LDHydro/meshslide/assets/20260126211406.jpg

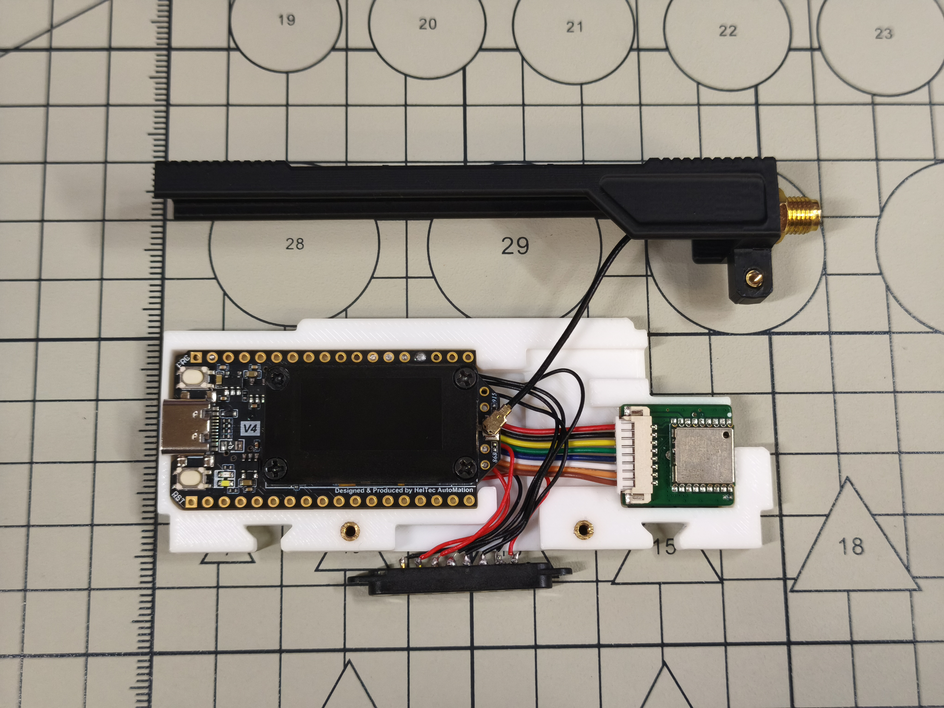
assets/20260126211406.jpg
