LDHydro/meshslide/assets/20260126212053.jpg

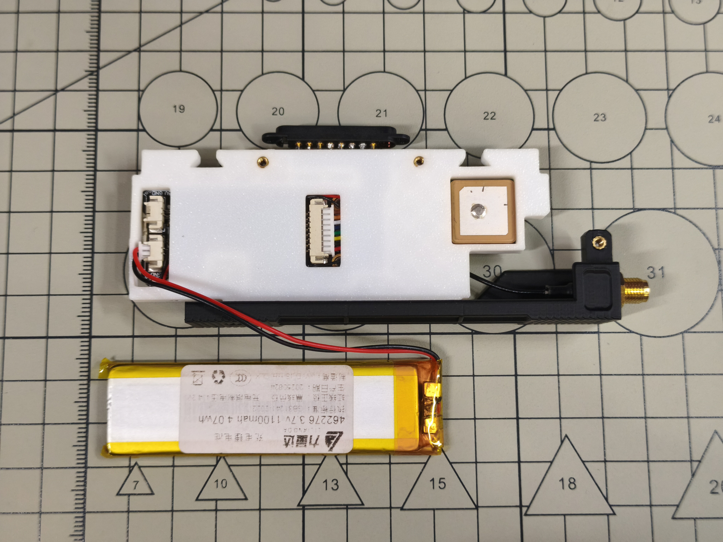
assets/20260126212053.jpg
