LDHydro/meshslide/assets/20260126212810.jpg

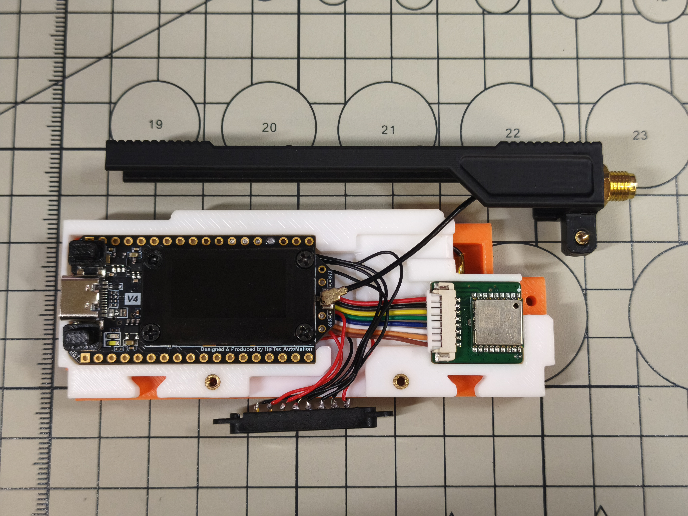
assets/20260126212810.jpg
