LDHydro/meshslide/assets/20260126213025.jpg

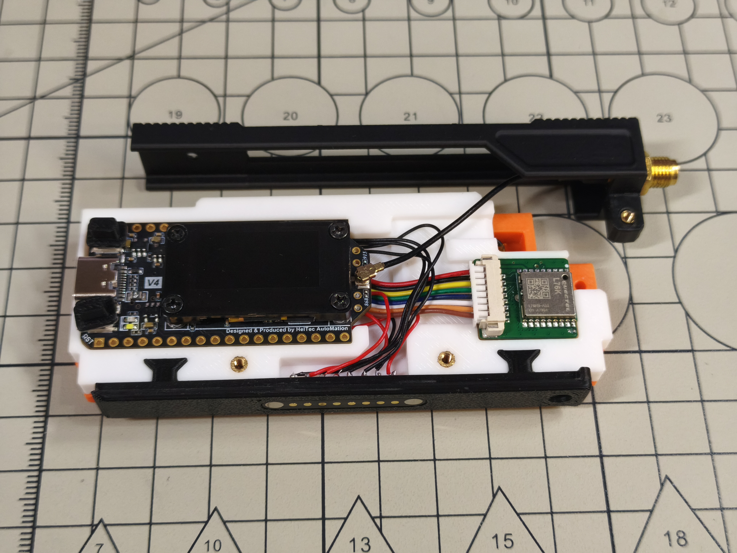
assets/20260126213025.jpg
