LDHydro/meshslide/assets/20260126222454.jpg

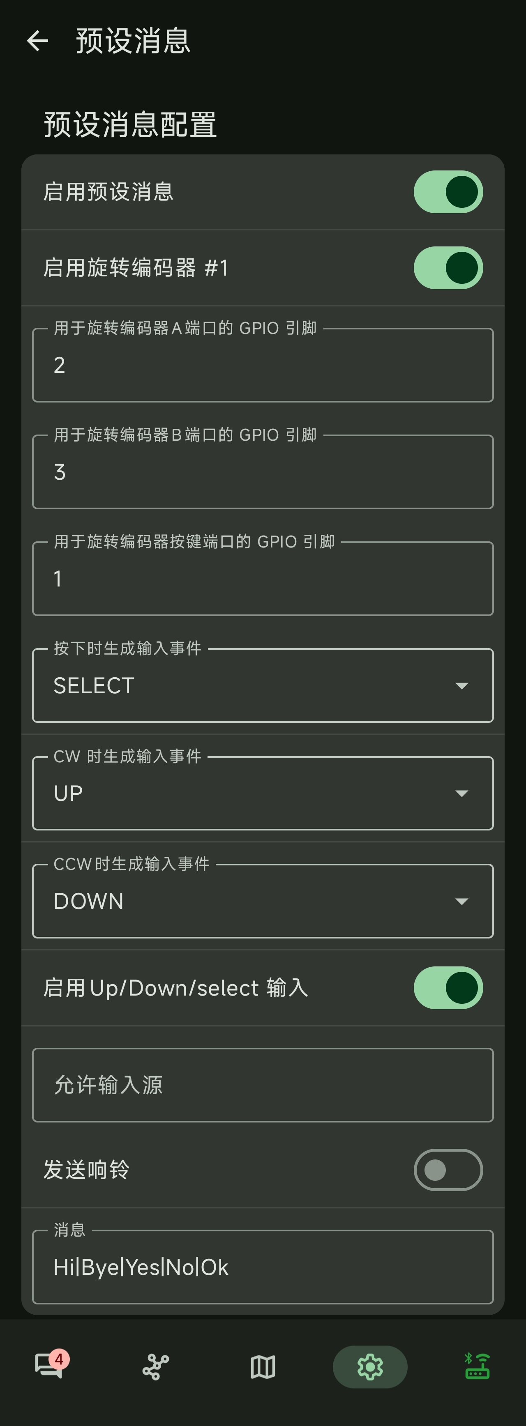
assets/20260126222454.jpg
