LDHydro/meshslide/assets/20260127204627.jpg

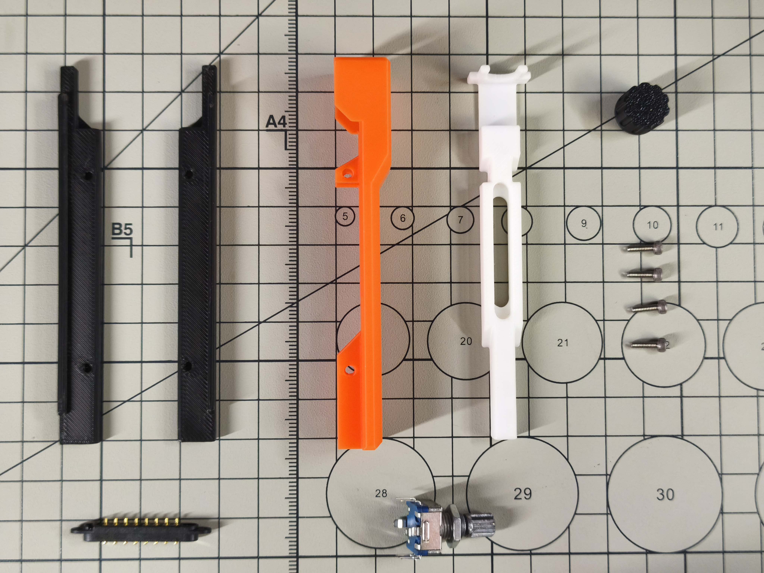
assets/20260127204627.jpg
