LDHydro/meshslide/assets/20260128224051.jpg

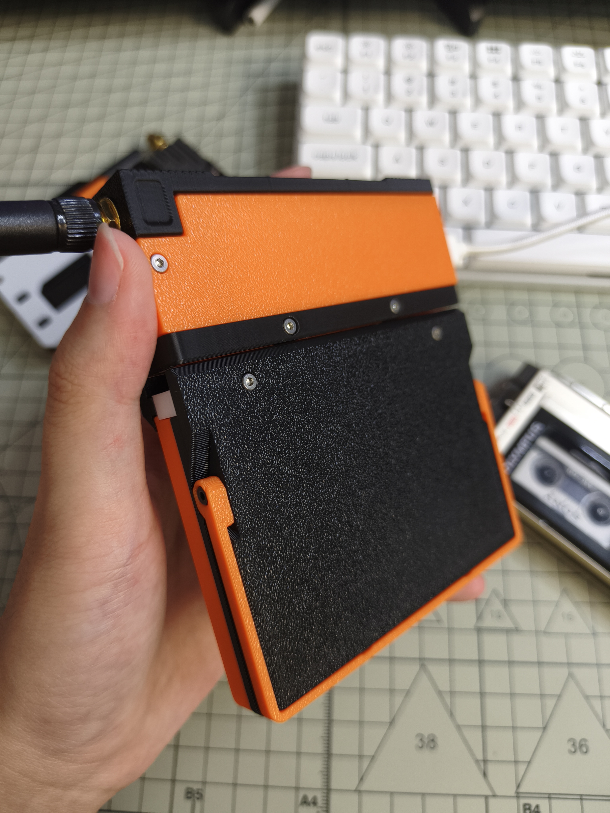
assets/20260128224051.jpg
