LDHydro/meshslide/assets/20260128224056.jpg

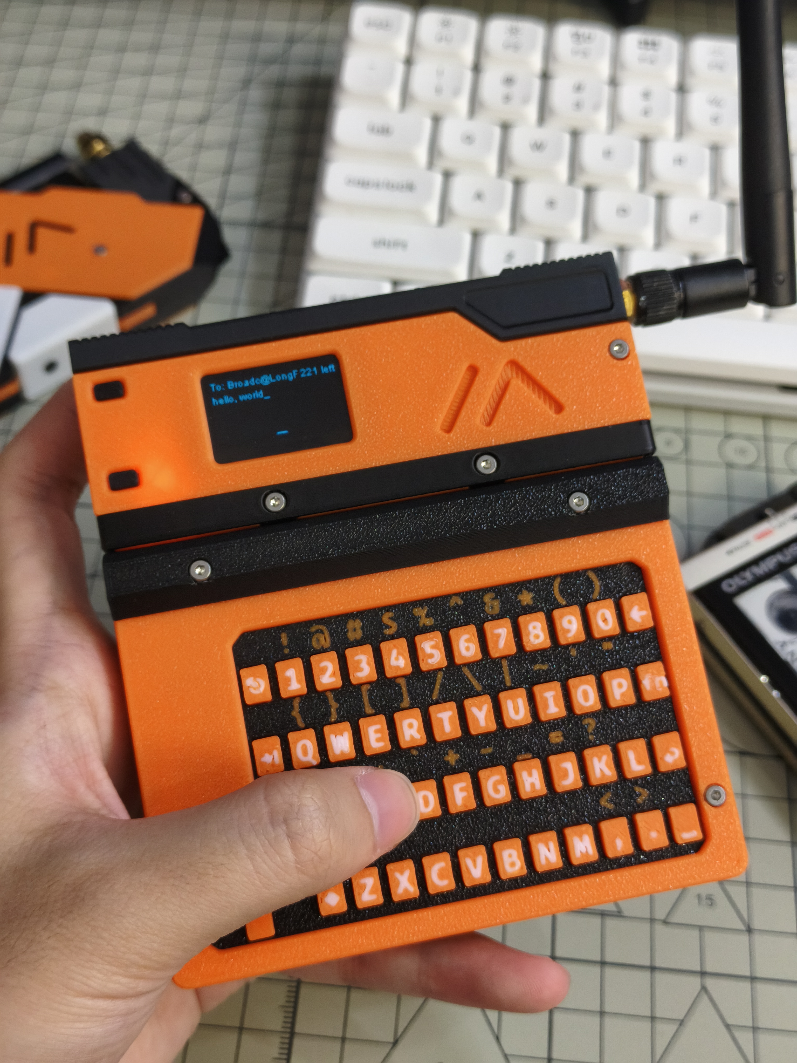
assets/20260128224056.jpg
