LDHydro/meshslide/assets/20260128224103.jpg

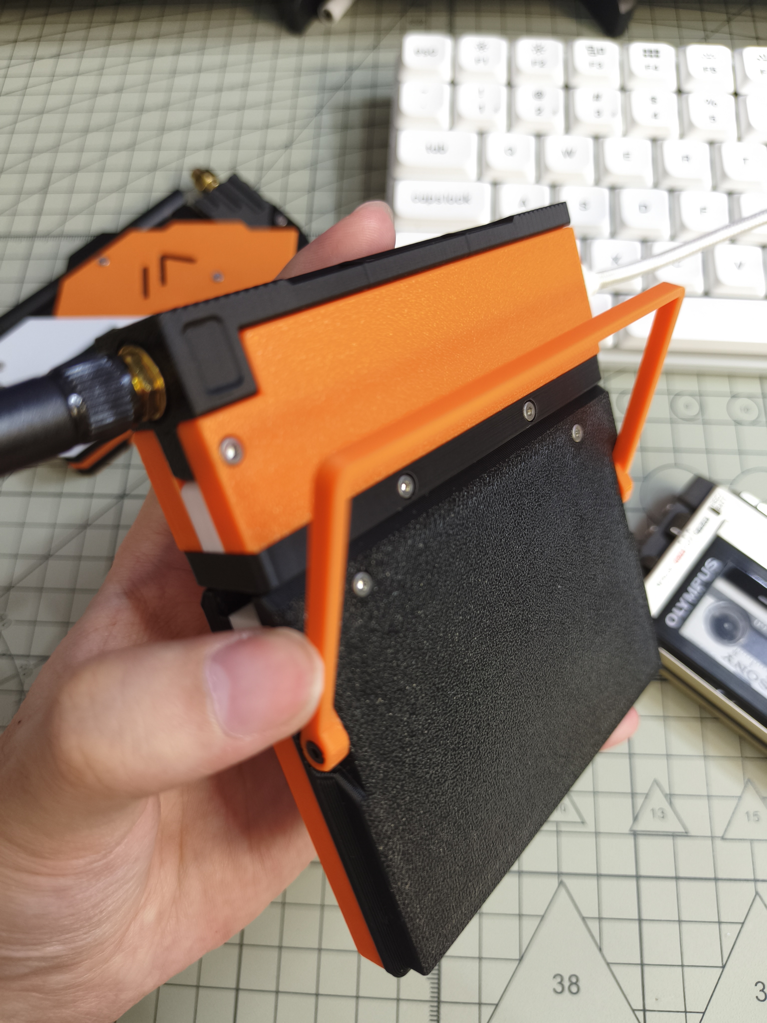
assets/20260128224103.jpg
