LDHydro/meshslide/assets/20260128224109.jpg

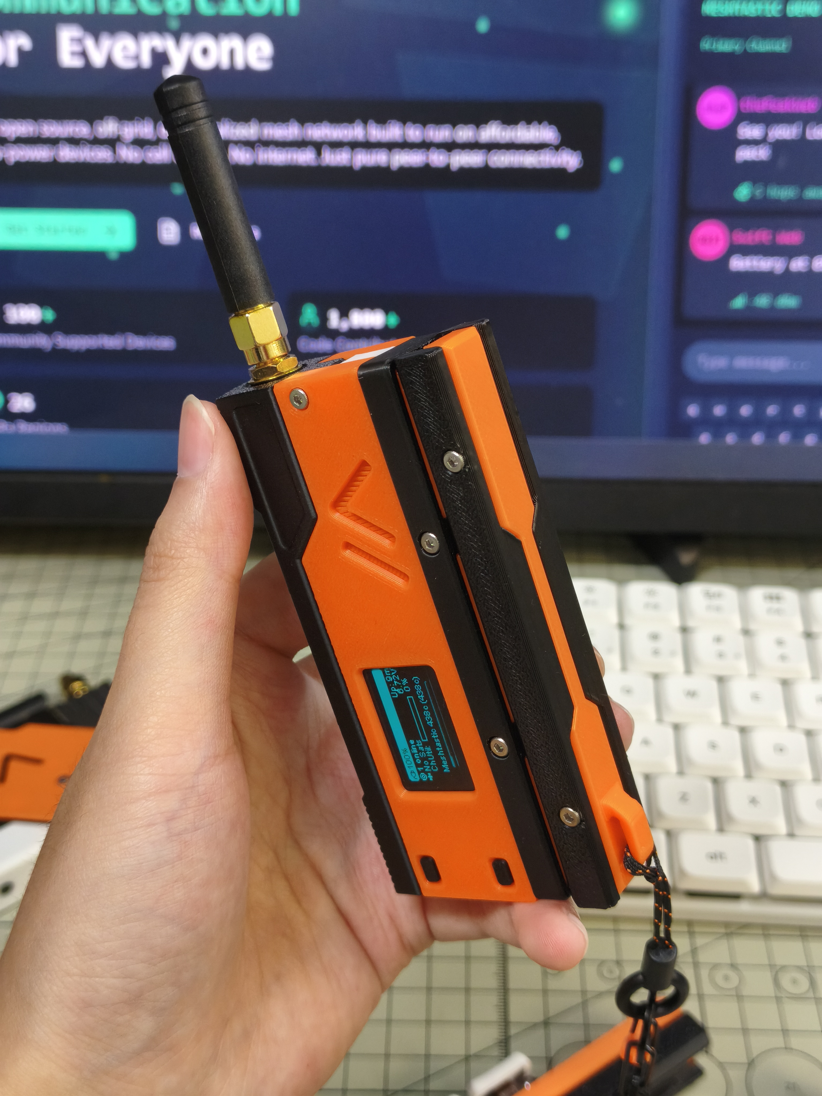
assets/20260128224109.jpg
