LDHydro/meshslide/assets/20260128224114.jpg

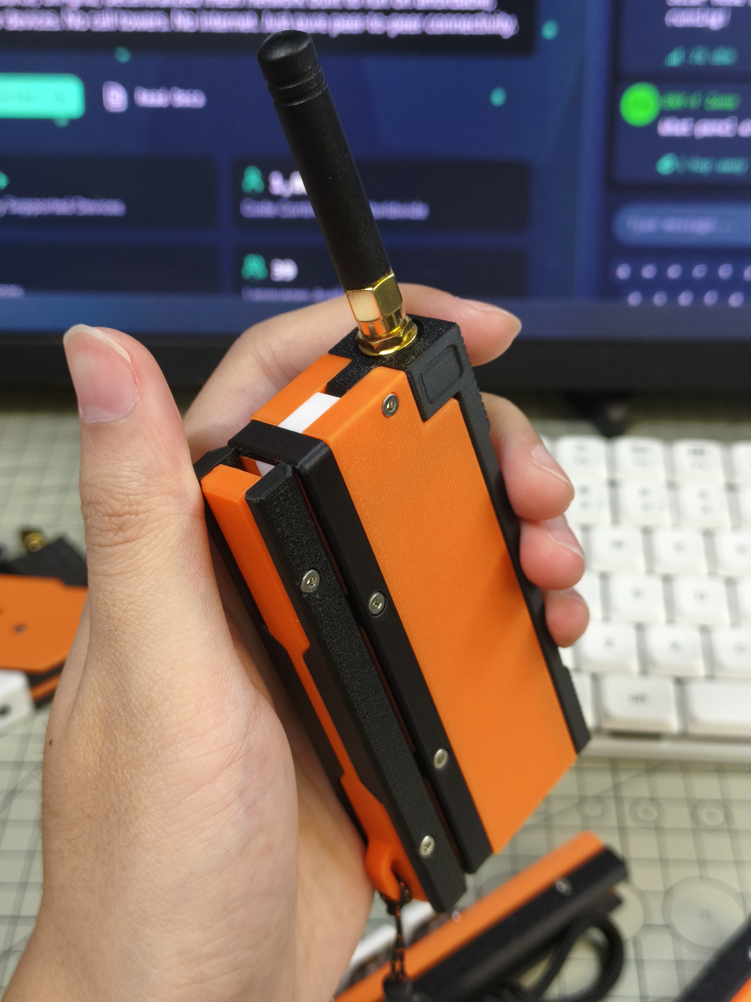
assets/20260128224114.jpg
