LDHydro/meshslide/assets/20260128224119.jpg

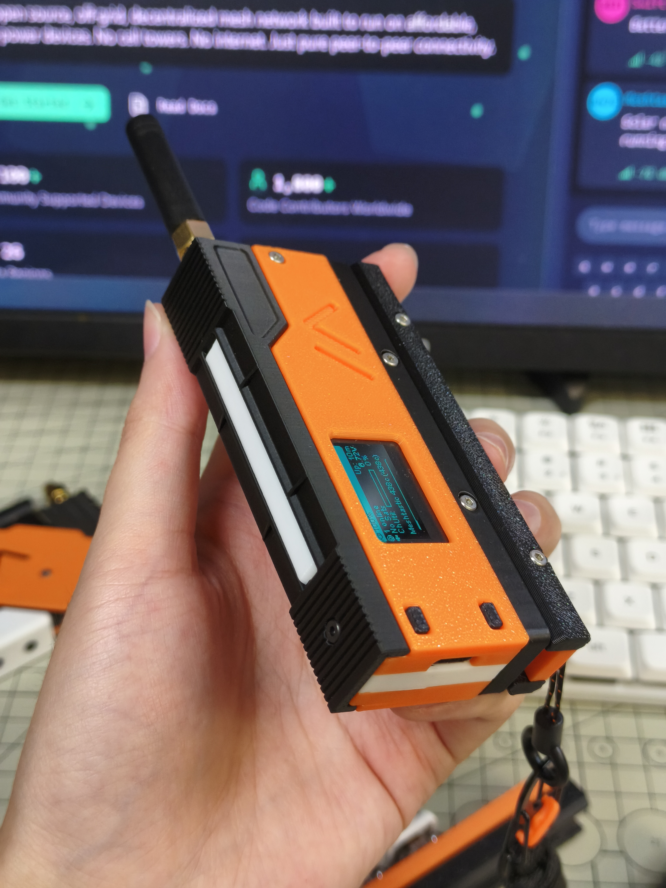
assets/20260128224119.jpg
