LDHydro/meshslide/assets/20260128224139.jpg

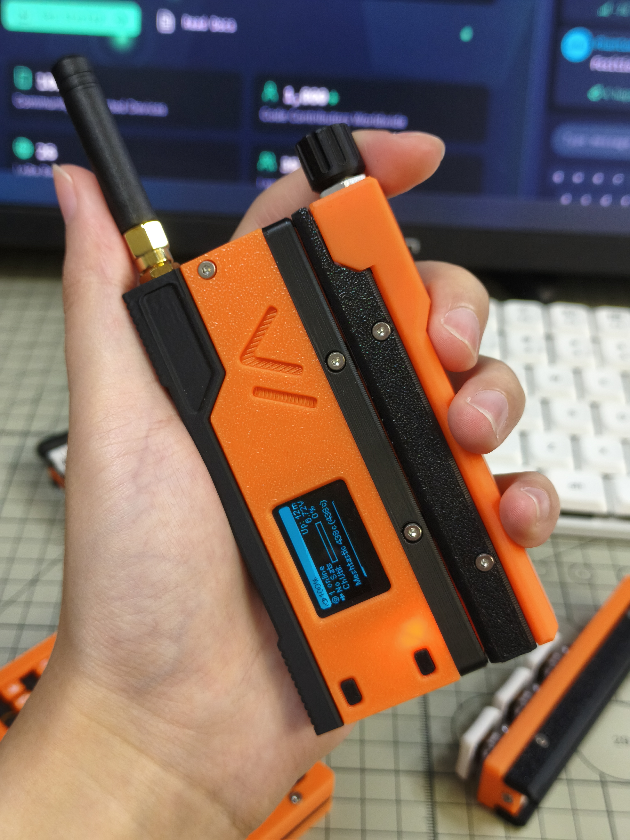
assets/20260128224139.jpg
