LDHydro/meshslide/assets/20260128224149.jpg

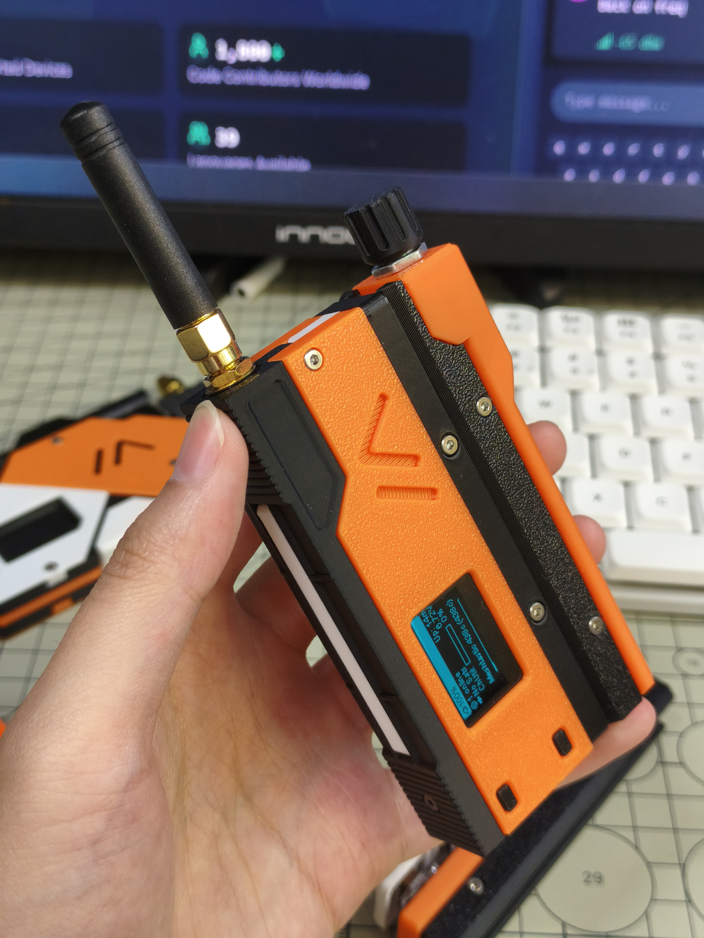
assets/20260128224149.jpg
