LDHydro/meshslide/assets/20260128224246.jpg

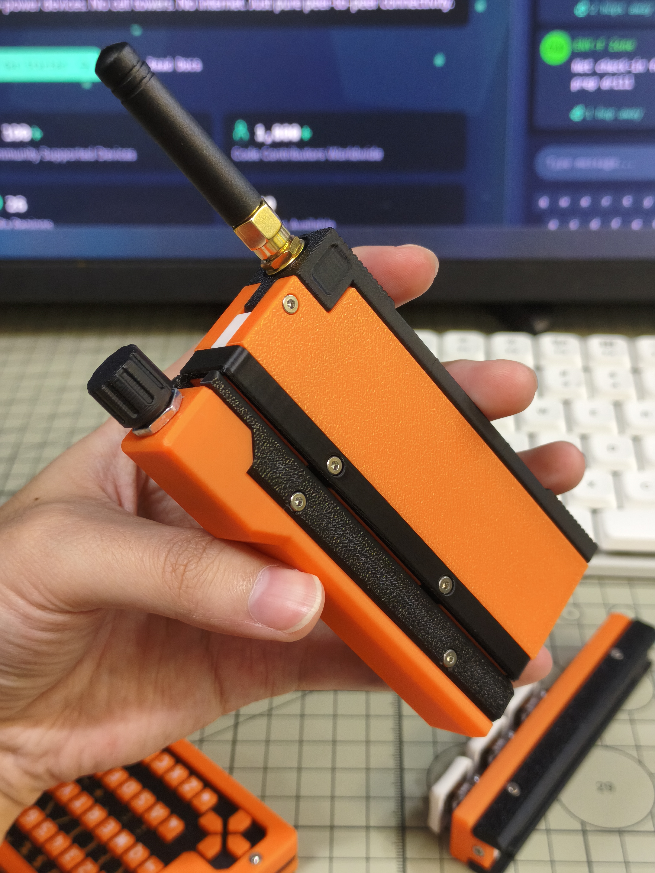
assets/20260128224246.jpg
