LDHydro/meshslide/assets/20260128224252.jpg

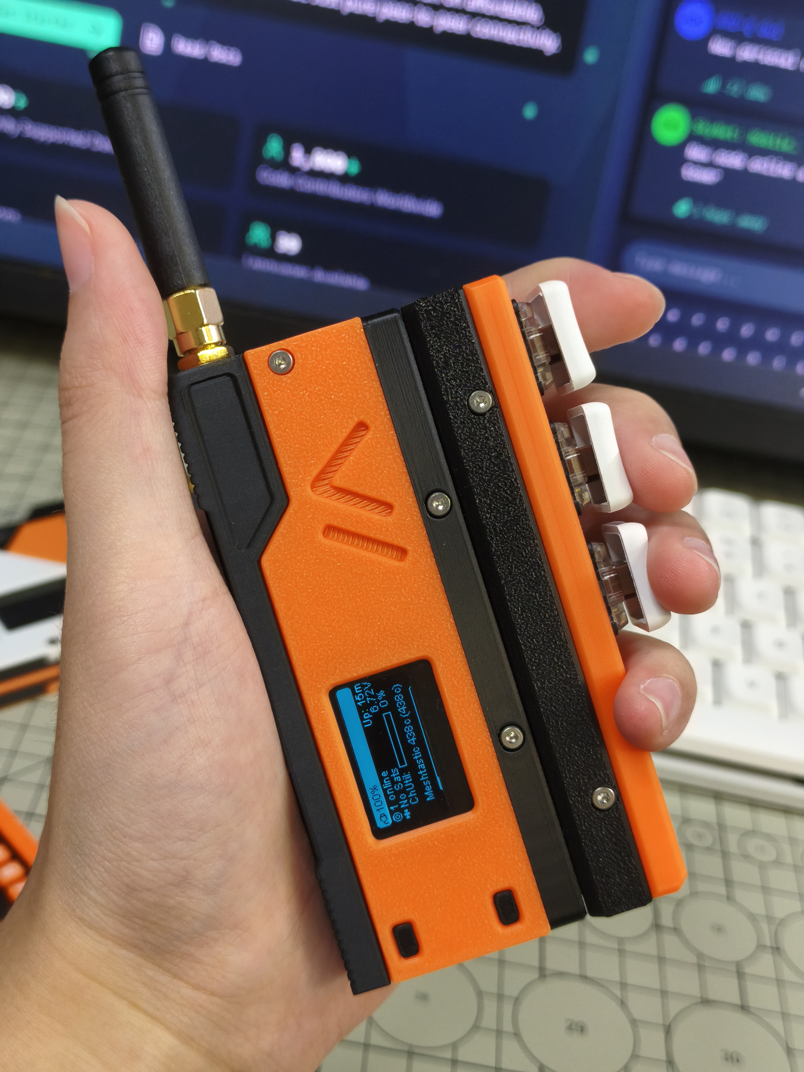
assets/20260128224252.jpg
