LDHydro/meshslide/assets/20260128224257.jpg

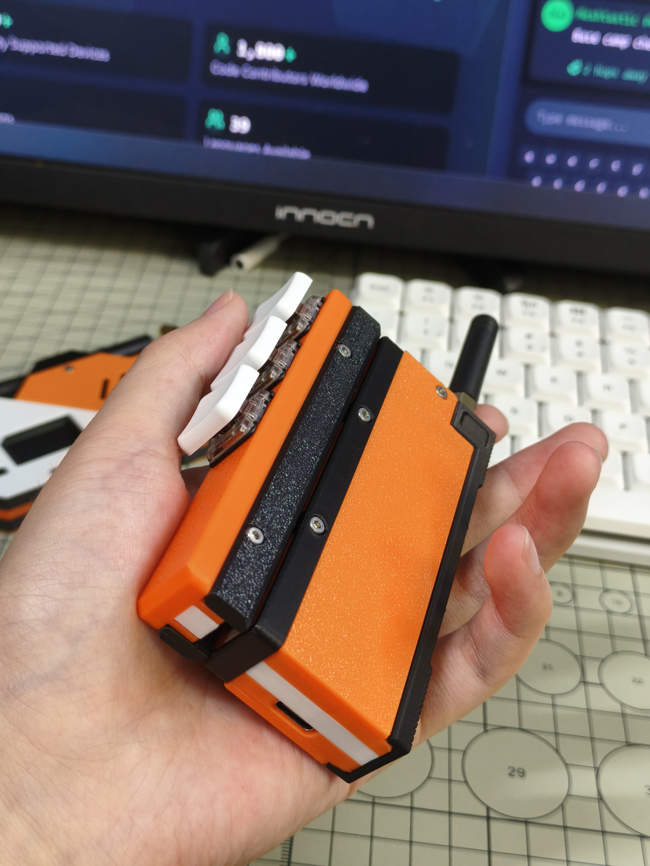
assets/20260128224257.jpg
