LDHydro/meshslide/assets/20260128224304.jpg

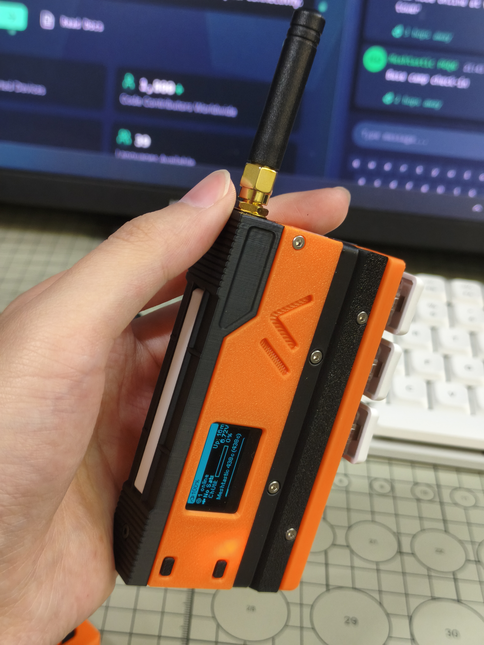
assets/20260128224304.jpg
