LDHydro/meshslide/assets/20260128224310.jpg

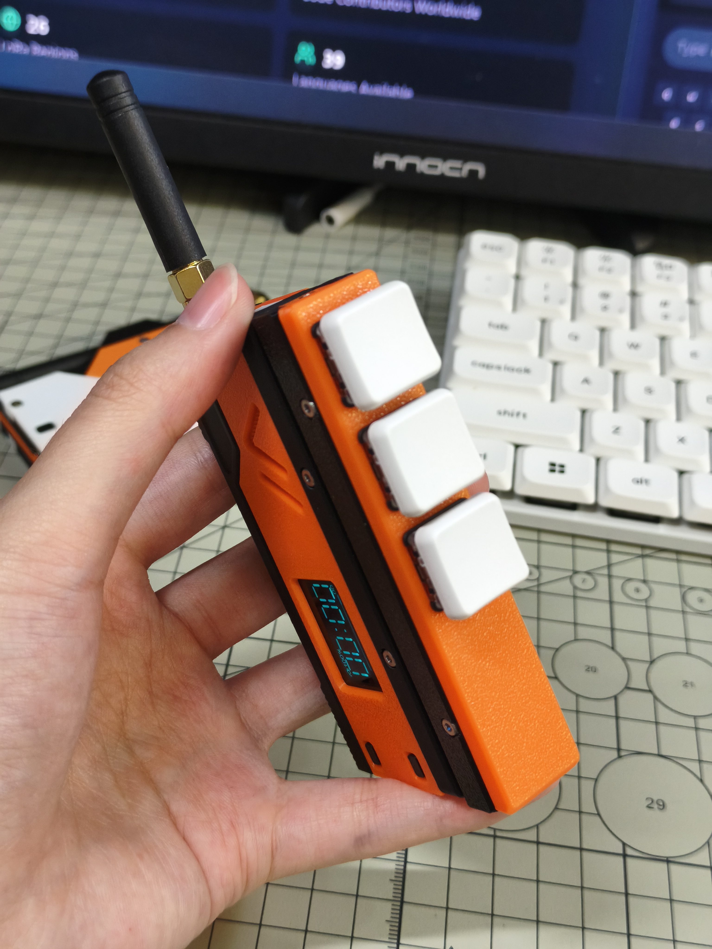
assets/20260128224310.jpg
