LDHydro/meshslide/assets/20260129183807.jpg

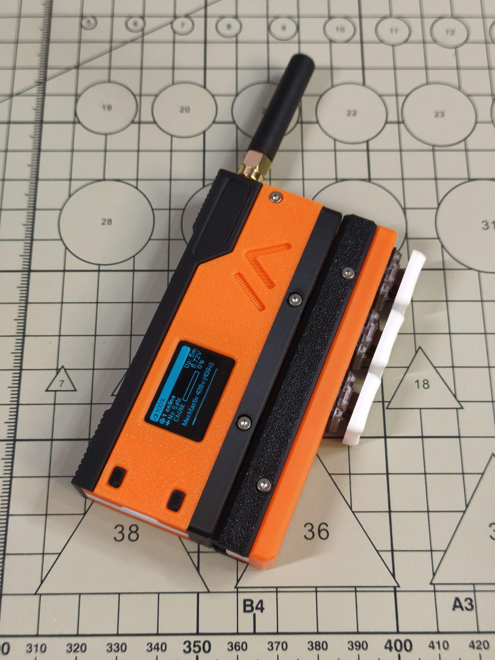
assets/20260129183807.jpg
