LDHydro/meshslide/assets/20260129183816.jpg

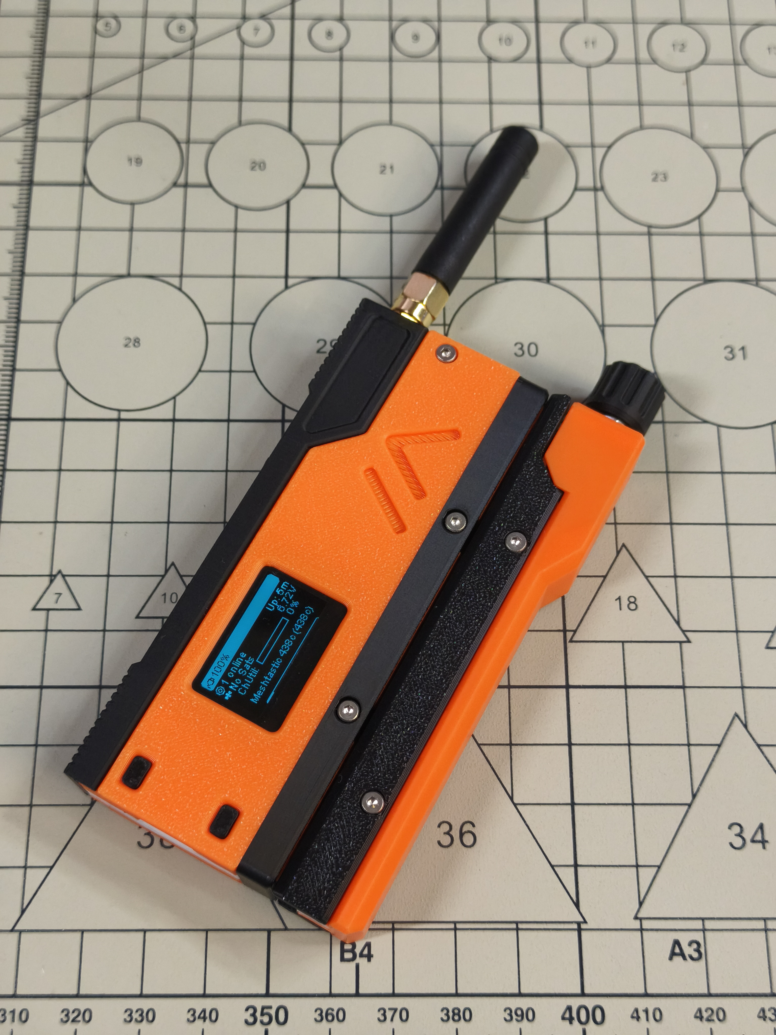
assets/20260129183816.jpg
