LDHydro/meshslide/assets/20260129183823.jpg

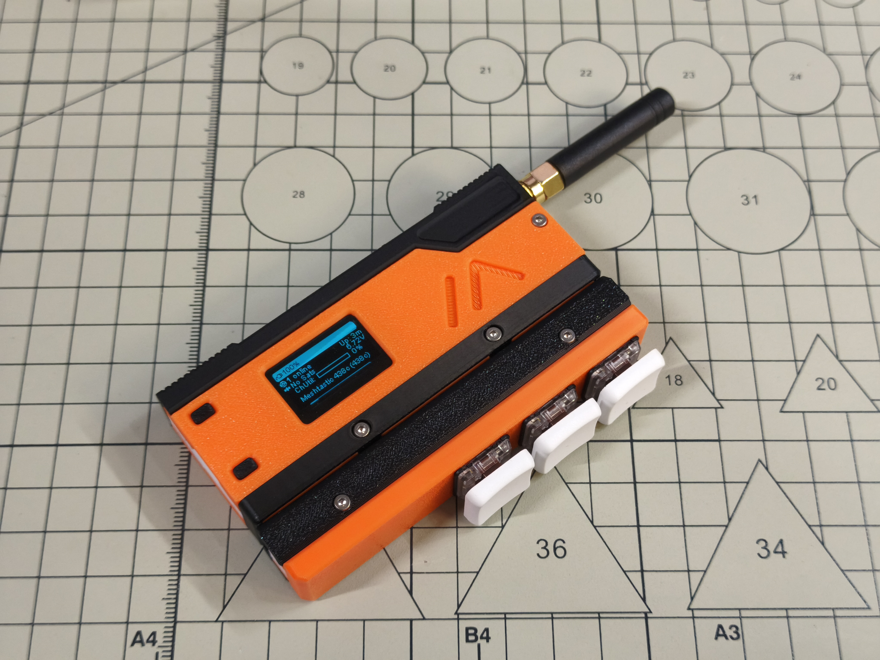
assets/20260129183823.jpg
