LDHydro/meshslide/assets/20260129183829.jpg

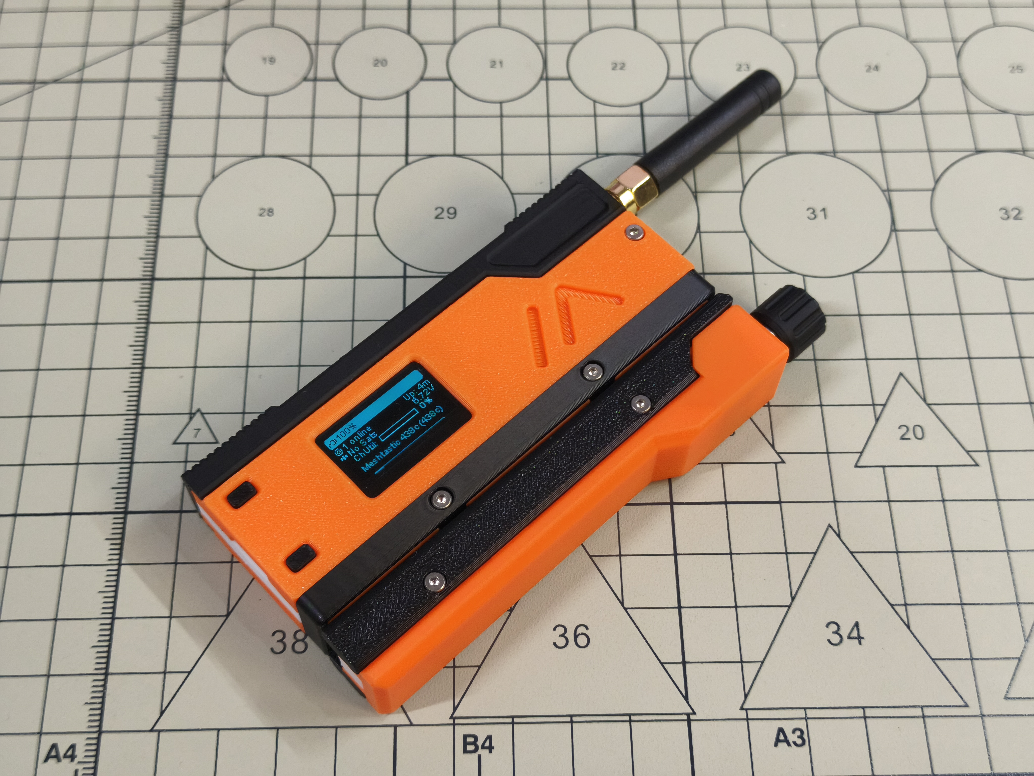
assets/20260129183829.jpg
