LDHydro/meshslide/assets/20260129185338.jpg

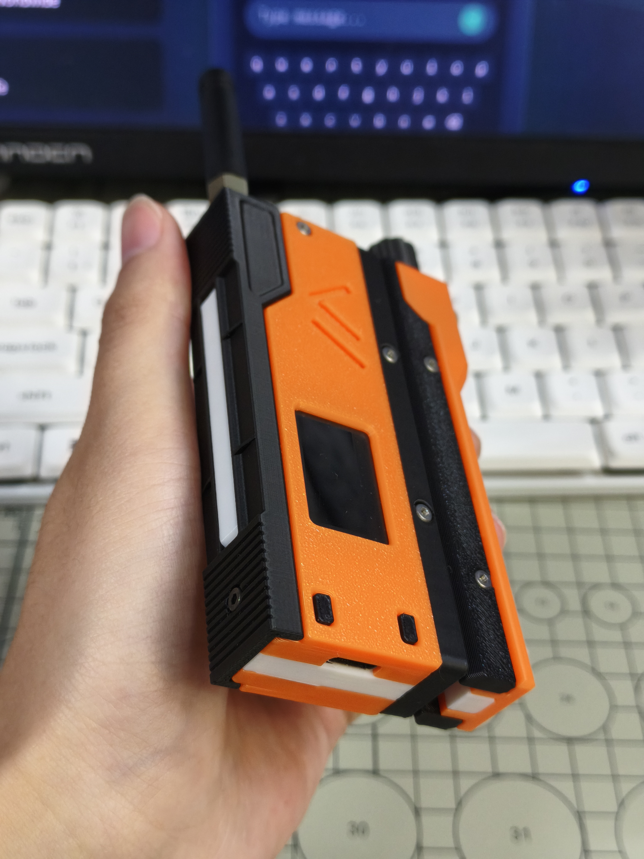
assets/20260129185338.jpg
