LDHydro/meshslide/Model/SlideRotary/RT_M1.SLDPRT

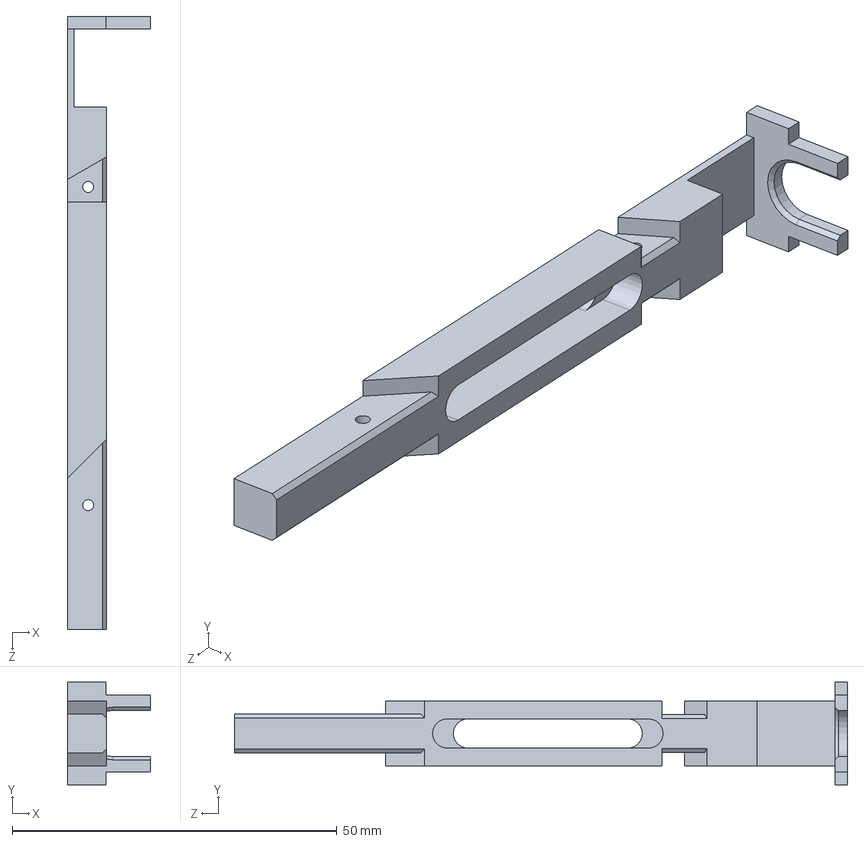
[picture p80: CAD file, 2026-01-29]
Model/SlideRotary/RT_M1.SLDPRT
12.8 x 15.8 x 94.4 mm
