LDHydro/meshslide/Model/SlideTriple/KS33-low profile.SLDPRT

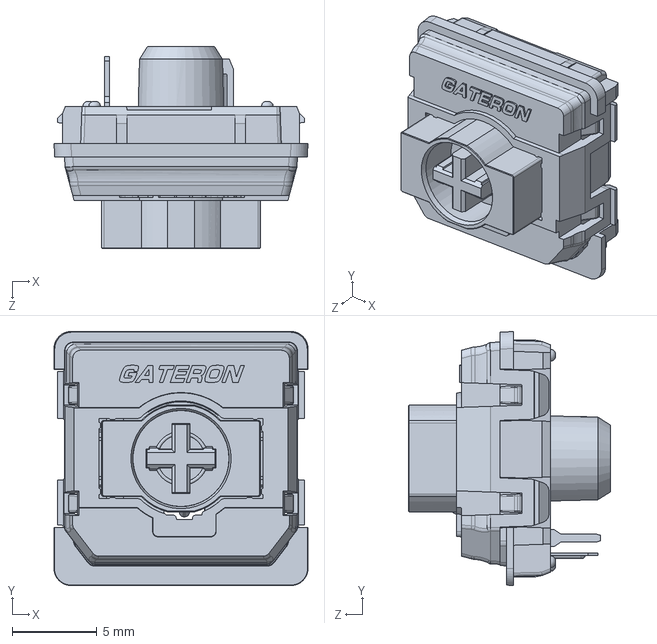
[picture p81: CAD file, 2026-01-29]
Model/SlideTriple/KS33-low profile.SLDPRT
15.0 x 15.0 x 11.9 mm
