LDHydro/meshslide/Model/SlideZero/SlideZero.STEP

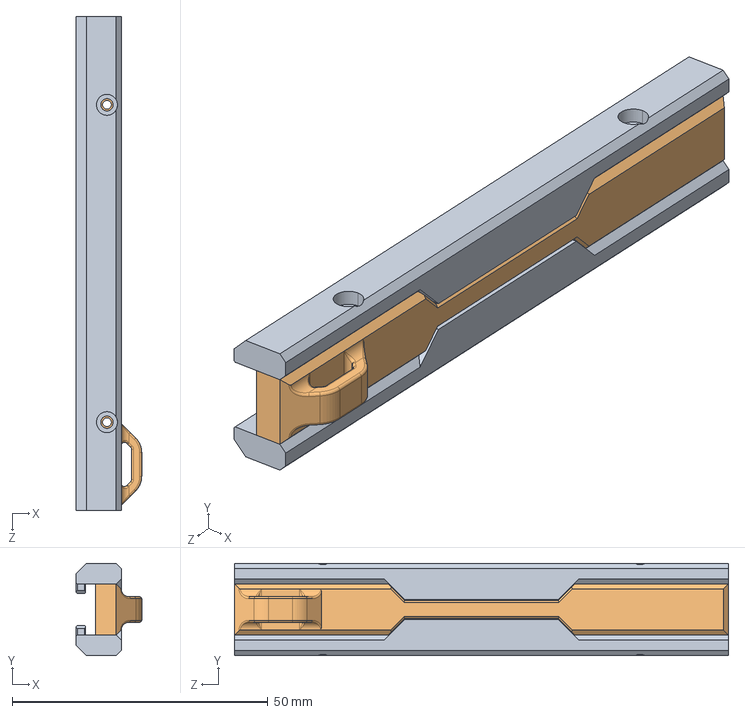
[picture p82: CAD file, 2026-01-29]
Model/SlideZero/SlideZero.STEP
12.8 x 18.0 x 96.5 mm
SZ_S2 x 2
SZ_M1
