LDHydro/meshslide/Model/CaseL1.SLDPRT

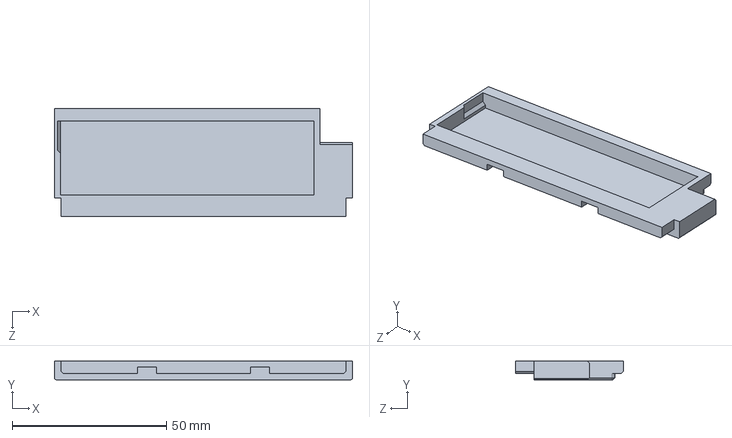
[picture p83: CAD file, 2026-03-21]
Model/CaseL1.SLDPRT
96.5 x 6.00 x 35.0 mm
