LDHydro/meshslide/Model/SlideKB/KB_S3.SLDPRT

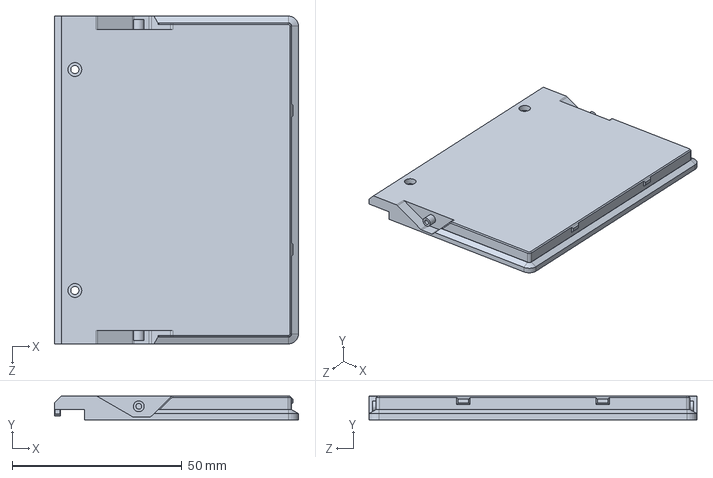
[picture p84: CAD file, 2026-01-29]
Model/SlideKB/KB_S3.SLDPRT
71.8 x 7.00 x 96.5 mm
