LDHydro/meshslide/Model/SlideRotary/RT_S1.SLDPRT

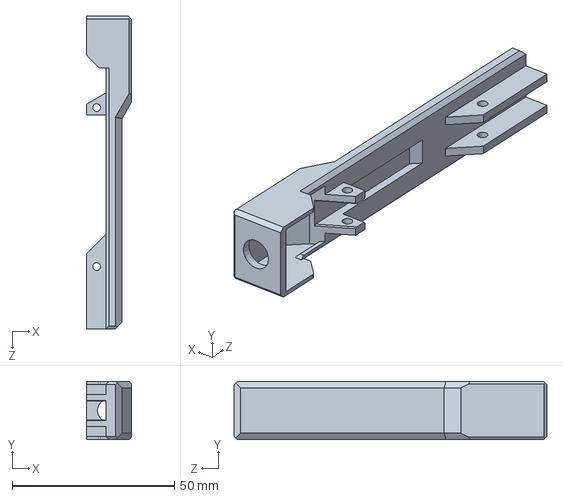
[picture p85: CAD file, 2026-01-29]
Model/SlideRotary/RT_S1.SLDPRT
14.0 x 18.0 x 96.5 mm
