LDHydro/meshslide/Model/SlideTriple/TP_M1.SLDPRT

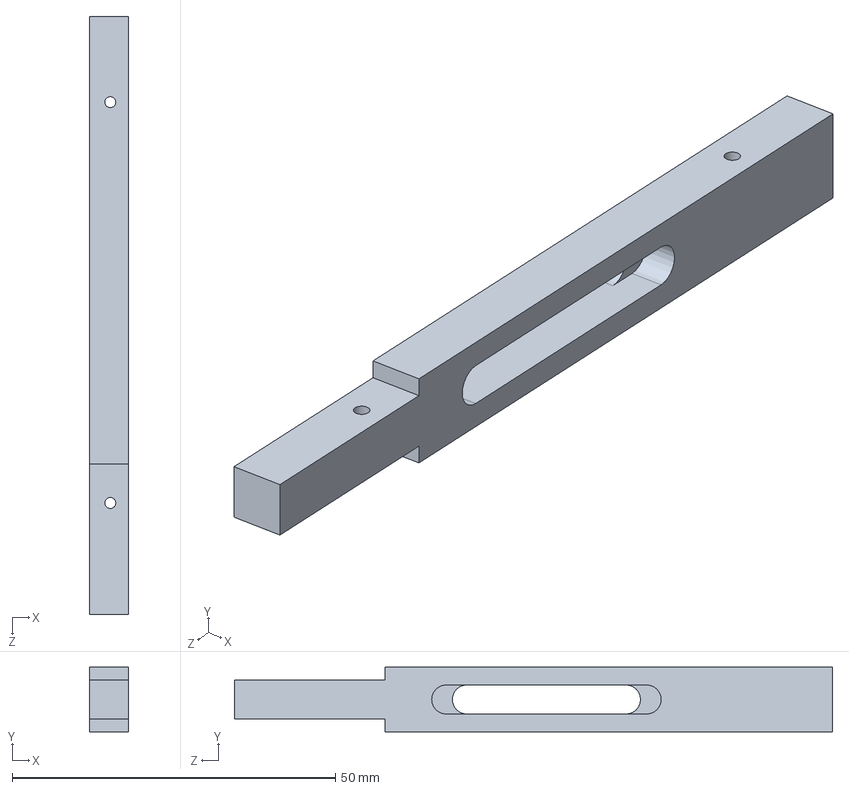
[picture p86: CAD file, 2026-01-29]
Model/SlideTriple/TP_M1.SLDPRT
6.00 x 10.0 x 92.5 mm
