LDHydro/meshslide/Model/SlideKB/KB_M1.SLDPRT

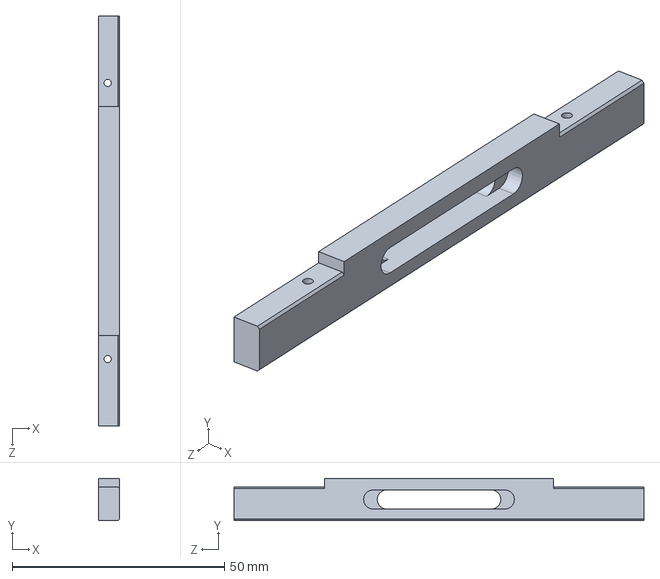
[picture p87: CAD file, 2026-01-29]
Model/SlideKB/KB_M1.SLDPRT
5.00 x 10.0 x 96.5 mm
