LDHydro/meshslide/Model/SlideRotary/EC11_Hat2.SLDPRT

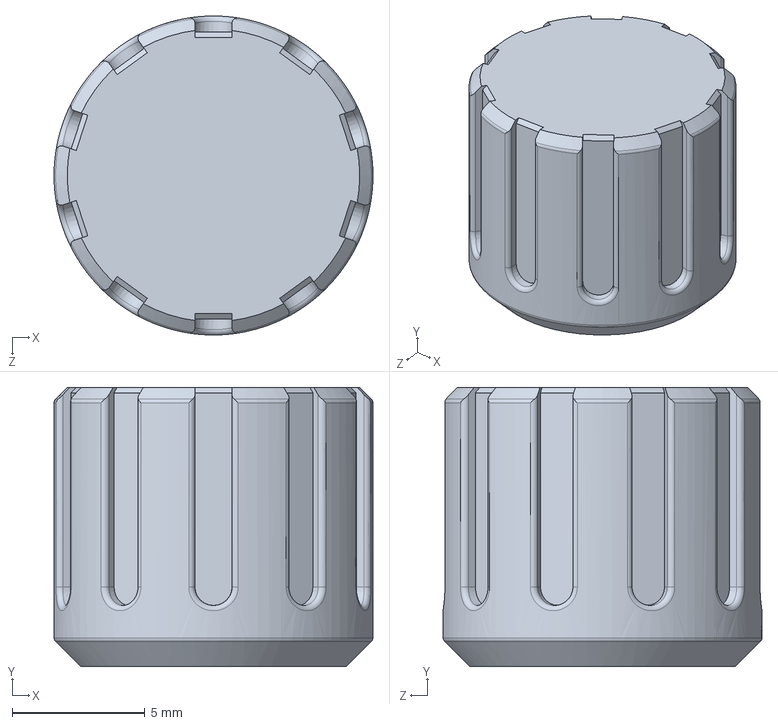
[picture p88: CAD file, 2026-01-29]
Model/SlideRotary/EC11_Hat2.SLDPRT
12.0 x 10.5 x 12.0 mm
