LDHydro/meshslide/Model/SlideTriple/TP_S1.SLDPRT

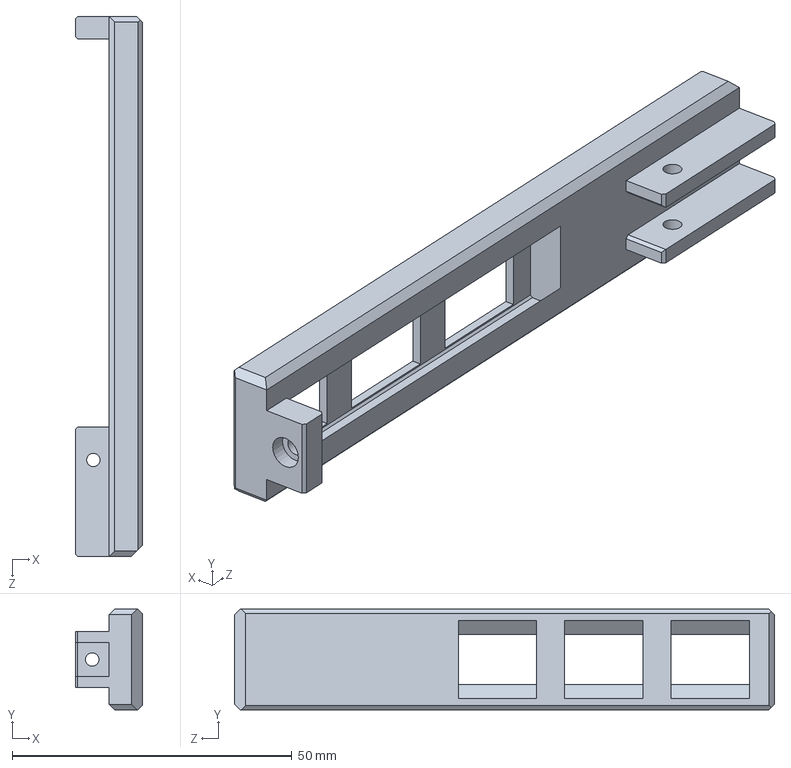
[picture p89: CAD file, 2026-01-29]
Model/SlideTriple/TP_S1.SLDPRT
12.0 x 18.0 x 96.5 mm
