LDHydro/meshslide/Model/SlideKB/KB_BTN.SLDPRT

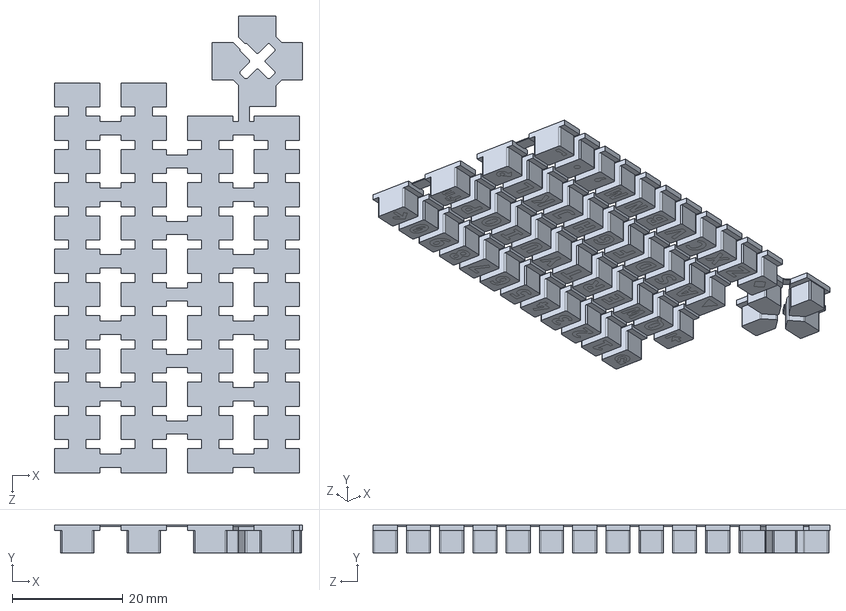
[picture p90: CAD file, 2026-01-29]
Model/SlideKB/KB_BTN.SLDPRT
44.8 x 5.00 x 82.5 mm
