LDHydro/meshslide/Model/SlideRotary/M7.SLDPRT

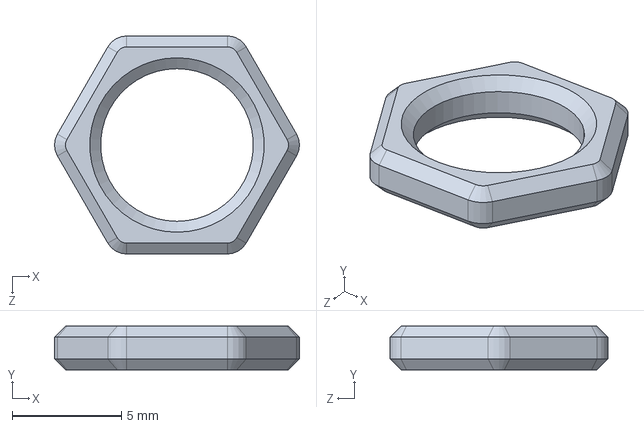
[picture p91: CAD file, 2026-01-29]
Model/SlideRotary/M7.SLDPRT
11.2 x 2.00 x 10.0 mm
