LDHydro/meshslide/Model/SMA_CAP.SLDPRT

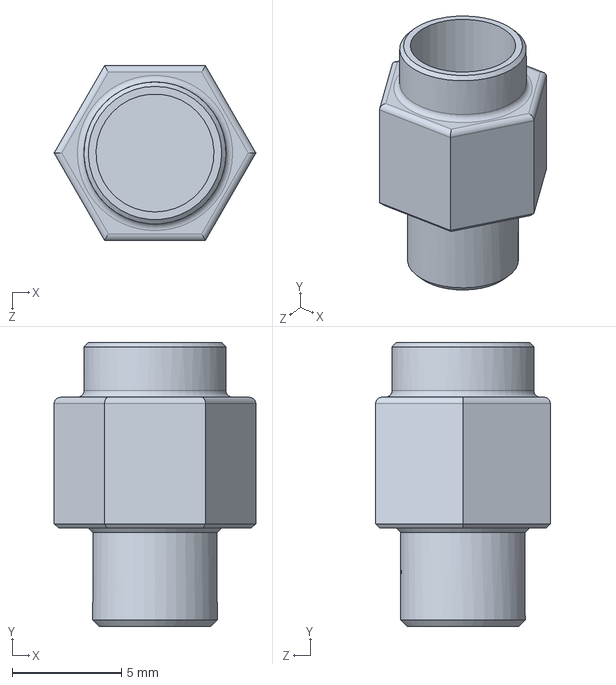
[picture p92: CAD file, 2026-01-29]
Model/SMA_CAP.SLDPRT
9.24 x 13.0 x 8.00 mm
