LDHydro/meshslide/Model/CaseSlide.SLDPRT

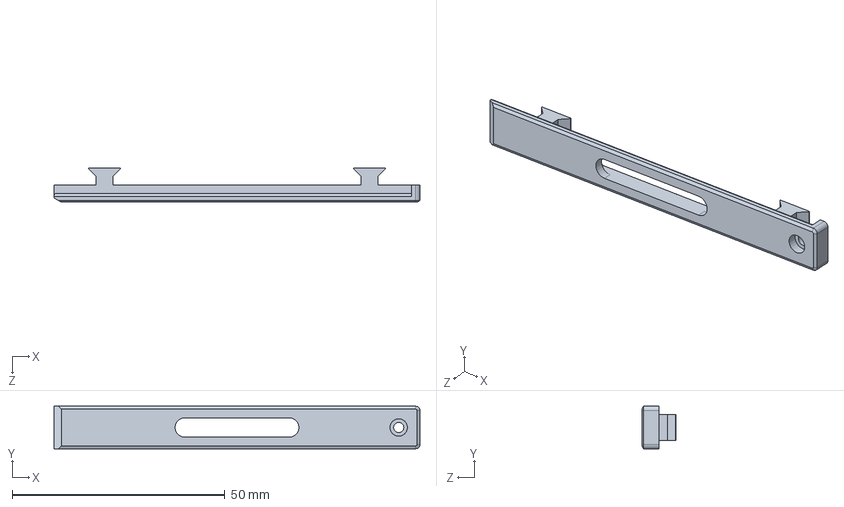
[picture p93: CAD file, 2026-01-29]
Model/CaseSlide.SLDPRT
86.0 x 10.0 x 8.10 mm
