LDHydro/meshslide/Model/SlideKB/KB_S2.SLDPRT

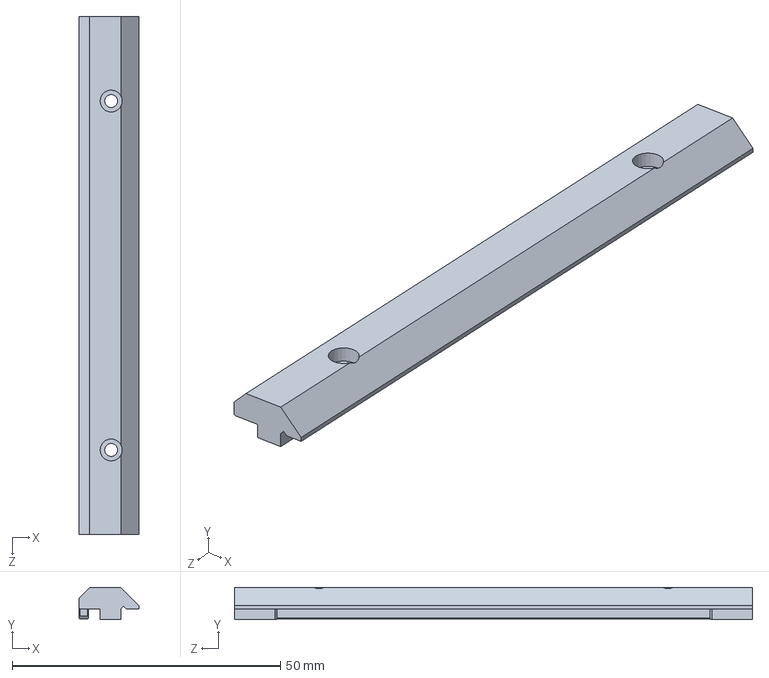
[picture p94: CAD file, 2026-01-29]
Model/SlideKB/KB_S2.SLDPRT
11.2 x 6.00 x 96.5 mm
