LDHydro/meshslide/Model/SlideRotary/RT_S2.SLDPRT

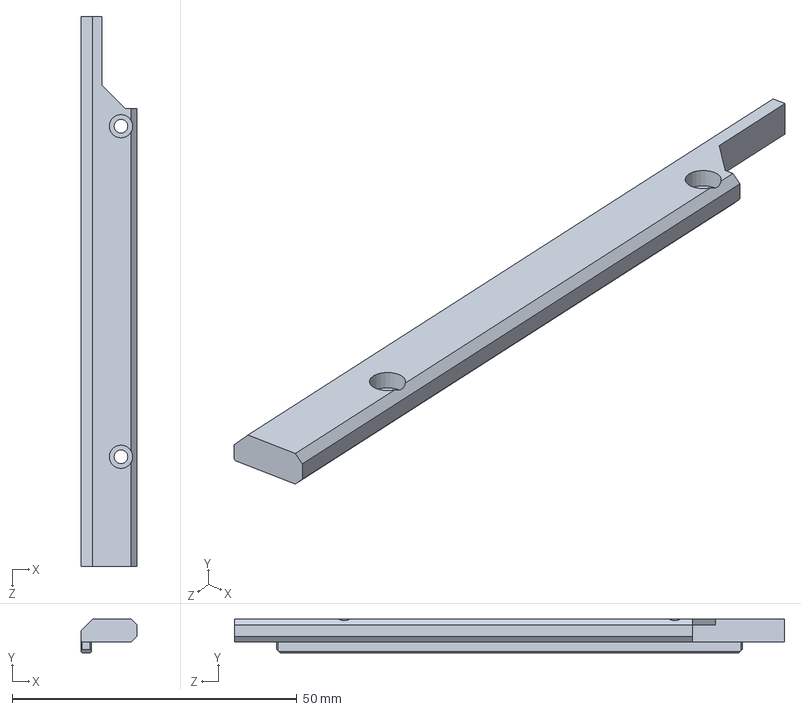
[picture p95: CAD file, 2026-01-29]
Model/SlideRotary/RT_S2.SLDPRT
9.80 x 5.90 x 96.5 mm
