LDHydro/meshslide/Model/SlideTriple/TP_S2.SLDPRT

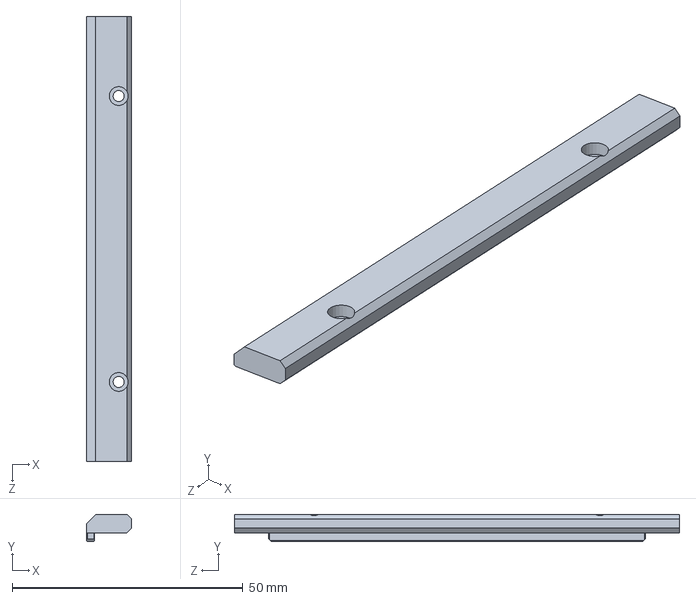
[picture p96: CAD file, 2026-01-29]
Model/SlideTriple/TP_S2.SLDPRT
9.80 x 5.90 x 96.5 mm
