LDHydro/meshslide/Model/SlideKB/KB_C1.SLDPRT

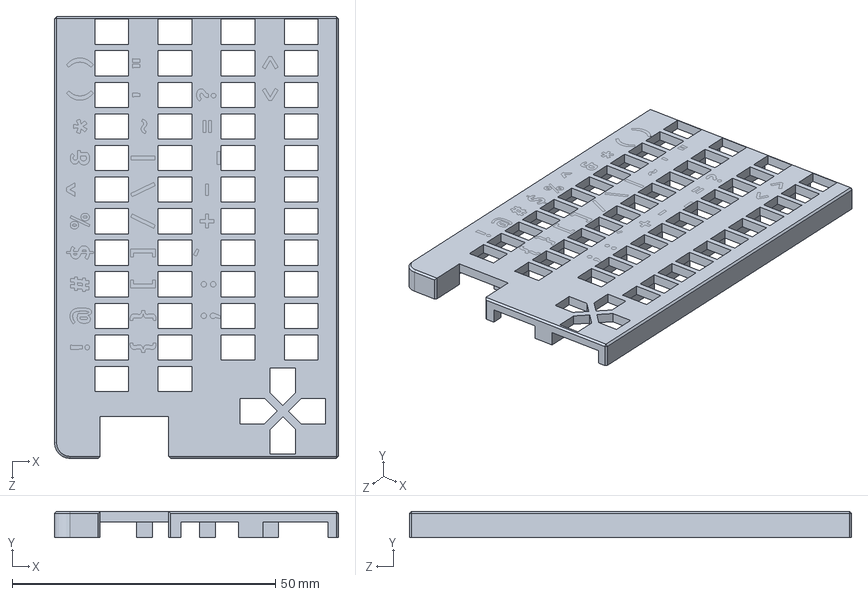
[picture p97: CAD file, 2026-01-29]
Model/SlideKB/KB_C1.SLDPRT
54.0 x 5.00 x 84.0 mm
