LDHydro/meshslide/Model/SlideRotary/SlideRotary.STEP

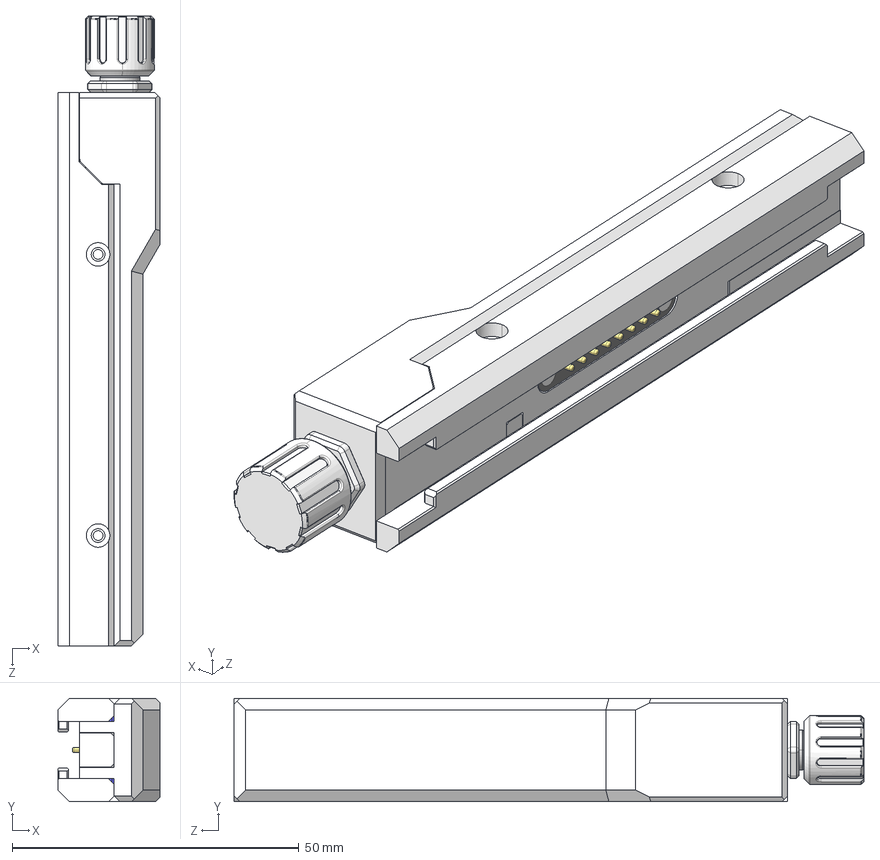
[picture p98: CAD file, 2026-01-29]
Model/SlideRotary/SlideRotary.STEP
17.8 x 18.0 x 109.8 mm
RT_S1
pogopin_8_B
RT_S2
RT_M1
M_RT_S2
M7
EC11 Rotary Encoder-15mm
EC11_Hat2
