LDHydro/meshslide/Model/SlideTriple/pogopin_8_B.SLDPRT

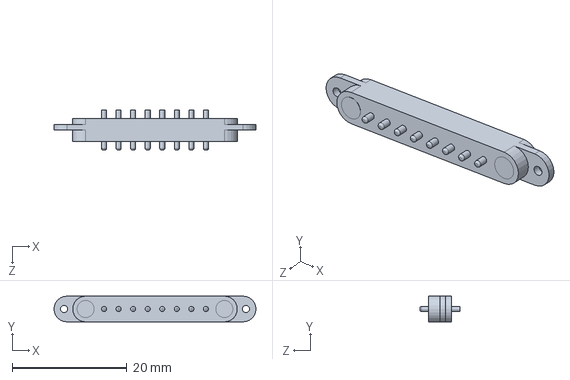
[picture p99: CAD file, 2026-01-29]
Model/SlideTriple/pogopin_8_B.SLDPRT
35.2 x 4.50 x 7.00 mm
