LDHydro/meshslide/Model/SlideRotary/EC11 Rotary Encoder-15mm.SLDPRT

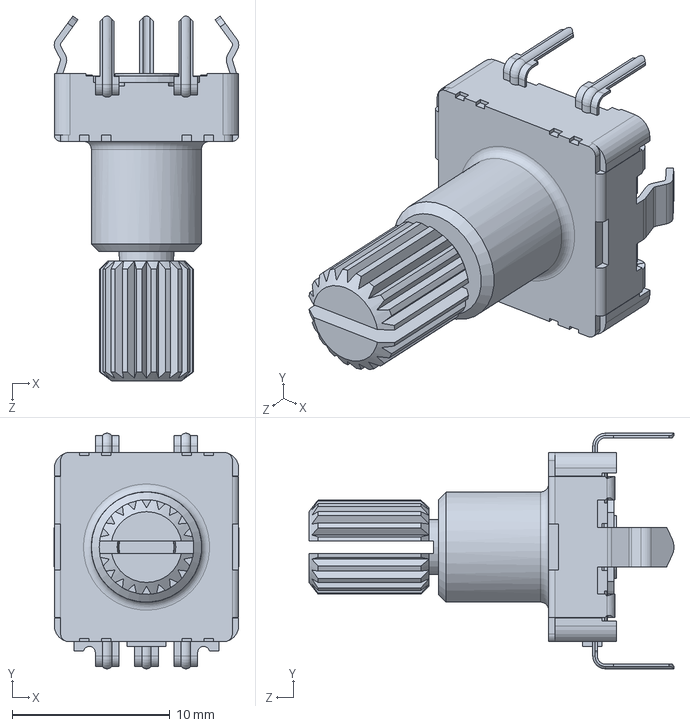
[picture p100: CAD file, 2026-01-29]
Model/SlideRotary/EC11 Rotary Encoder-15mm.SLDPRT
11.7 x 14.9 x 23.2 mm
