LDHydro/meshslide/Model/battery.SLDPRT

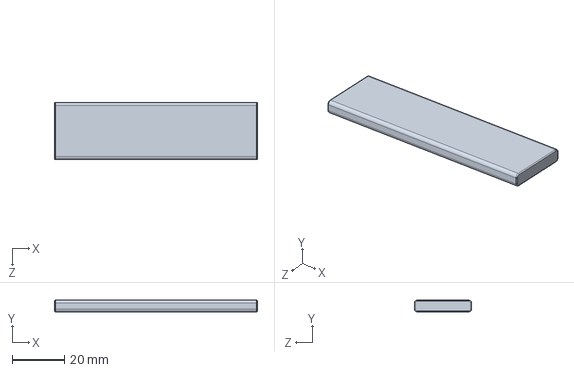
[picture p101: CAD file, 2026-01-29]
Model/battery.SLDPRT
78.0 x 4.60 x 22.0 mm
