LDHydro/meshslide/Model/pogopin_8_A.SLDPRT

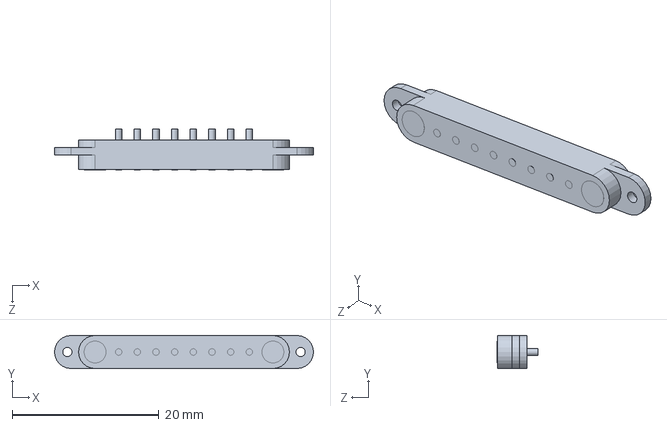
[picture p102: CAD file, 2026-01-29]
Model/pogopin_8_A.SLDPRT
35.2 x 4.50 x 5.52 mm
