LDHydro/meshslide/Model/GNSS.SLDPRT

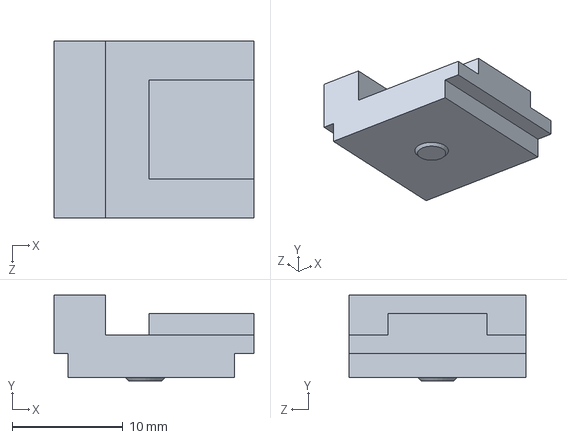
[picture p103: CAD file, 2026-01-29]
Model/GNSS.SLDPRT
18.1 x 7.74 x 16.0 mm
