LDHydro/meshslide/Model/CaseS1.SLDPRT

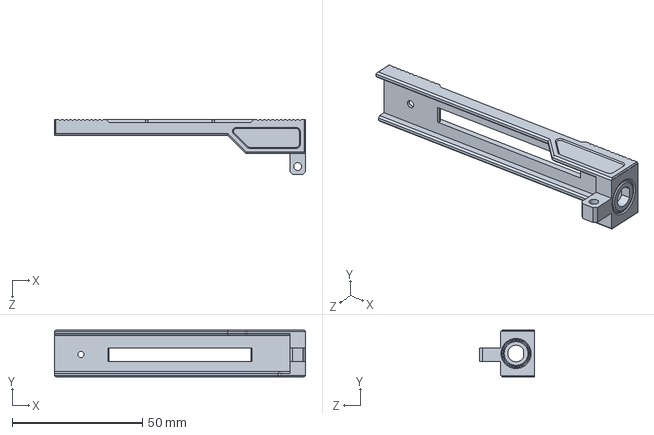
[picture p104: CAD file, 2026-01-29]
Model/CaseS1.SLDPRT
96.5 x 18.0 x 21.0 mm
