LDHydro/meshslide/Model/tm-2024a.SLDPRT

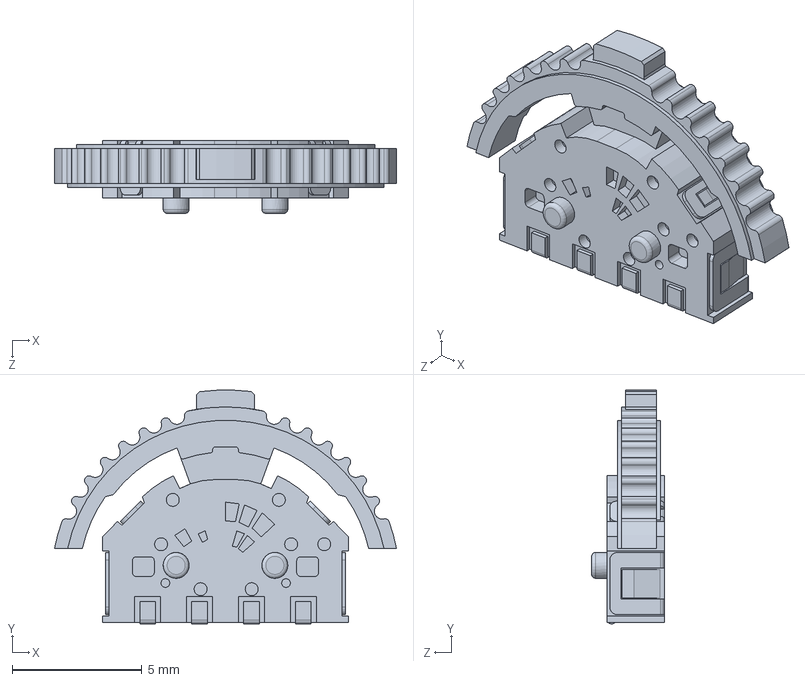
[picture p105: CAD file, 2026-01-29]
Model/tm-2024a.SLDPRT
13.2 x 8.99 x 2.80 mm
