LDHydro/meshslide/Model/CaseButton.SLDPRT

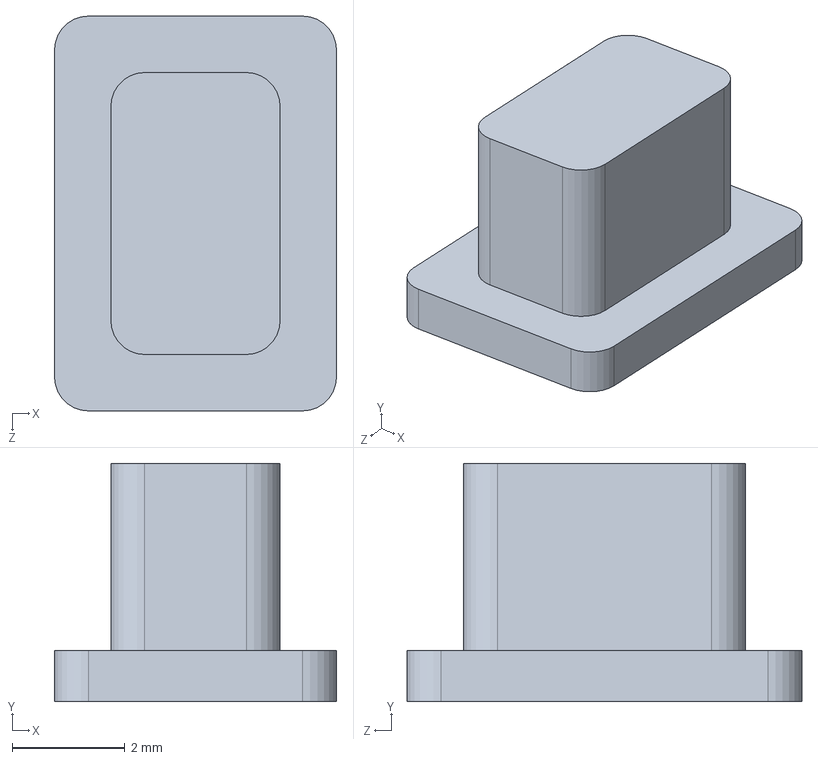
[picture p106: CAD file, 2026-01-29]
Model/CaseButton.SLDPRT
5.00 x 4.22 x 7.00 mm
