LDHydro/meshslide/Model/CaseR1.SLDPRT

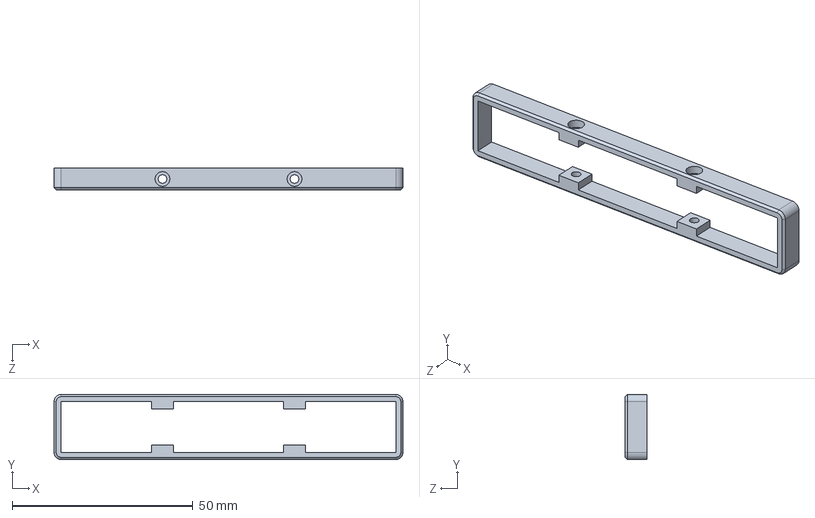
[picture p107: CAD file, 2026-01-29]
Model/CaseR1.SLDPRT
96.5 x 18.0 x 6.00 mm
