LDHydro/meshslide/Model/Antenna.SLDPRT

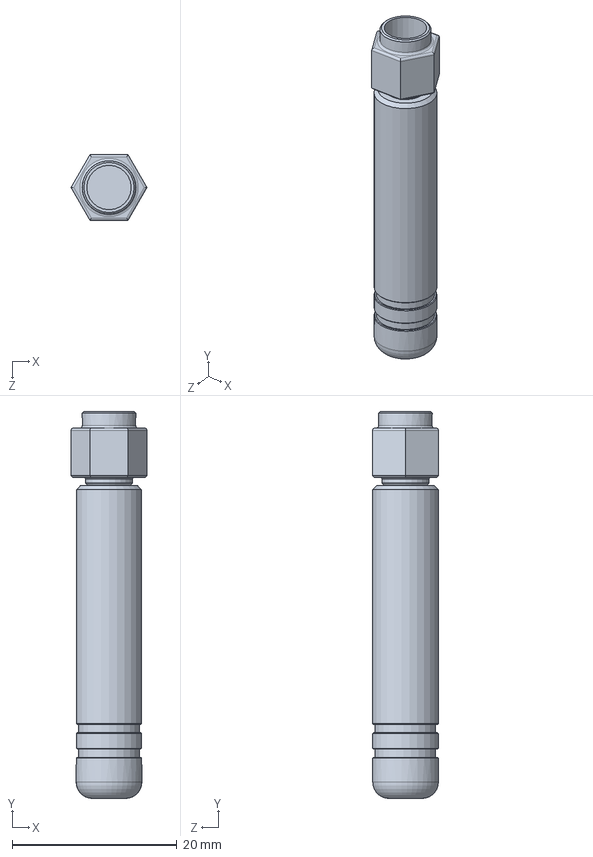
[picture p108: CAD file, 2026-01-29]
Model/Antenna.SLDPRT
9.24 x 47.0 x 8.00 mm
