LDHydro/meshslide/assets/20260126202707.jpg

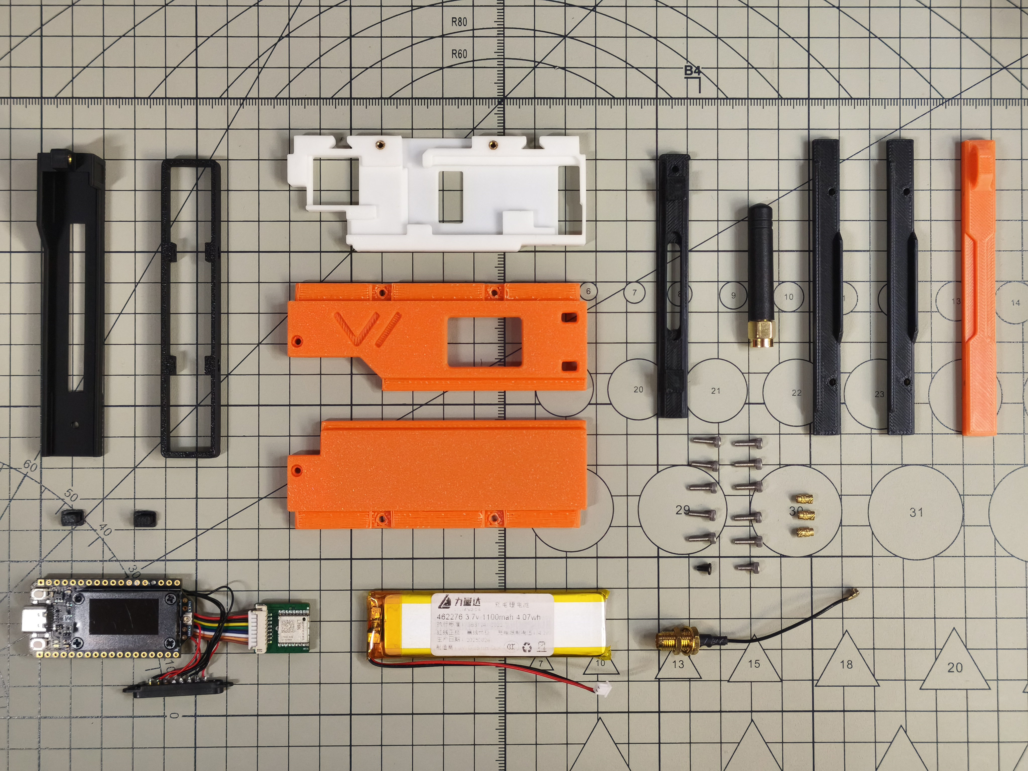
assets/20260126202707.jpg
